abeednaz/R56-Mini-MFD/PCBs/OBD port power distribution board/V2.7-Connector-board/Untitled.jpg

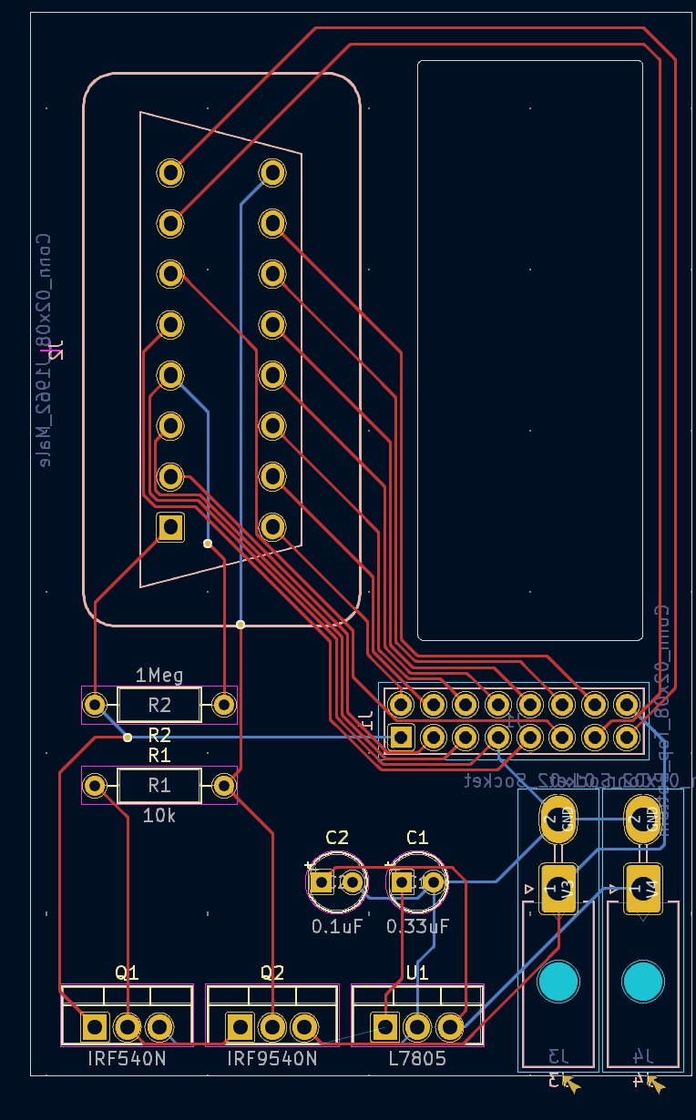
PCBs/OBD port power distribution board/V2.7-Connector-board/Untitled.jpg
