abeednaz/R56-Mini-MFD/Reference/Arduino pre compile settings.jpg

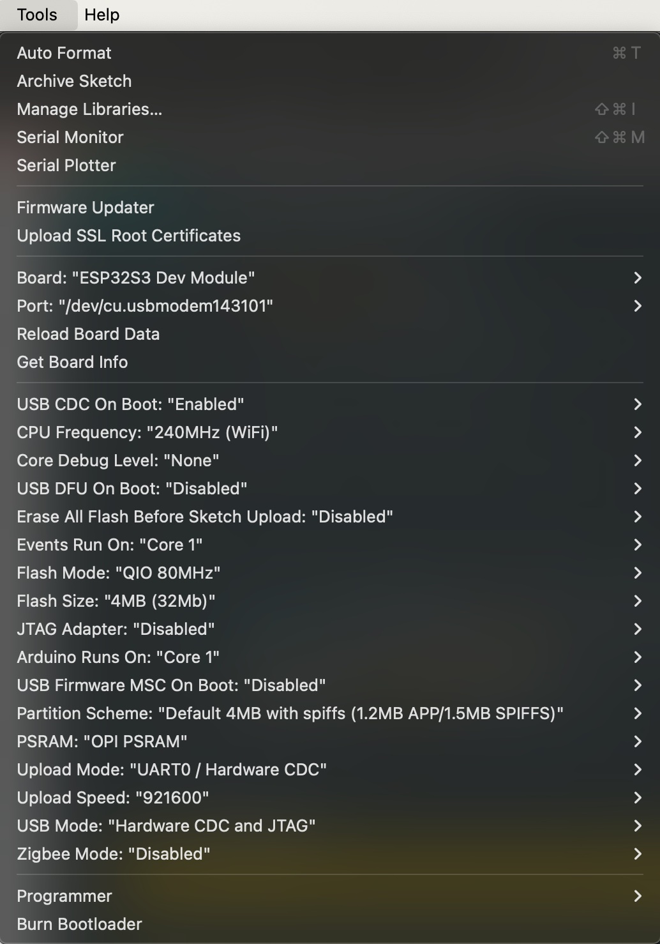
Reference/Arduino pre compile settings.jpg
