abeednaz/R56-Mini-MFD/Reference/Gauge images/Font/numbers.jpg

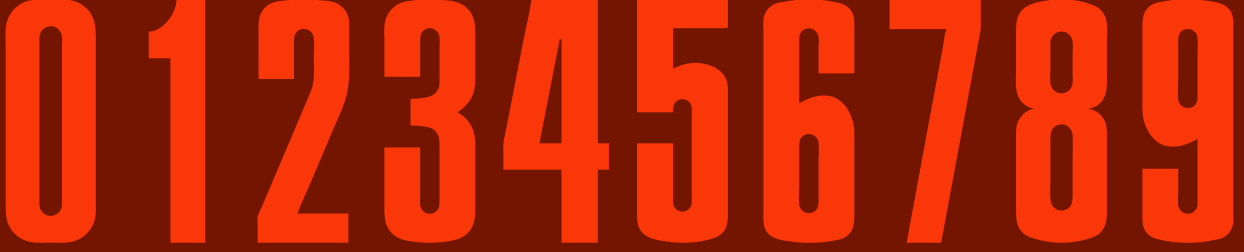
Reference/Gauge images/Font/numbers.jpg
