abeednaz/R56-Mini-MFD/PCBs/OBD port power distribution board/Simulation/MOSFET switch sim.asc

M1: pmos; IRF7343P
M2: nmos; IRF530
R1: res; 10k
R2: Res; 1Meg
R_load: Res; 50
SPDT: spdt
V1: voltage; PWL(0 12 4 12 4.01 0 7 0)
V_bat: voltage; 12
V_ign: voltage; PWL(0 0 1 0 1.01 12 2 12 2.01 0 3 0 5 0 5.01 12 6 12 6.01 0 7 0)
Named nets: 0, V_Load, V_trig, V_ign2, V_bat_sw
*.dc V_ign 0 12 0.01
.tran 7
.plot V(V_Load)
.subckt SPDT COM NO NC POS NEG
S1 COM NO POS NEG MYSW1
S2 COM NC NEG POS MYSW2
.model MYSW1 SW(Ron=.01 Roff=1000Meg Vh=.25 Vt=.5)
.model MYSW2 SW(Ron=.01 Roff=1000Meg Vh=.25 Vt=-.5)
.ends
